JakeFriesen/6502_computer/keyboard_lib.asm

;-----------------------------------------------;
;              Keyboard Library                 ;
;-----------------------------------------------;

; Keyboard pointers
kb_wptr = $0000
kb_rptr = $0001
kb_flags = $0002

; 256-byte kb buffer 0200-02ff
kb_buffer = $0200  


key_pressed:
  ldx kb_rptr
  lda kb_buffer, x
  cmp #$0a           ; enter - go to second line
  beq enter_pressed
  cmp #$1b           ; escape - clear display
  beq esc_pressed

  jsr print_char
  
  lda kb_buffer, x    ;load it again for acia
  jsr print_char_acia

  inc kb_rptr
  jmp loop

enter_pressed:
  lda #%10101000 ; put cursor at position 40
  jsr lcd_instruction
  inc kb_rptr
  jmp loop

esc_pressed:
  lda #%00000001 ; Clear display
  jsr lcd_instruction
  inc kb_rptr
  jmp loop

; IRQ vector points here
keyboard_interrupt:
  pha
  txa
  pha
  lda kb_flags
  and #RELEASE   ; check if we're releasing a key
  beq read_key   ; otherwise, read the key

  lda kb_flags
  eor #RELEASE   ; flip the releasing bit
  sta kb_flags
  lda PORTA      ; read key value that's being released
  cmp #$12       ; left shift
  beq shift_up
  cmp #$59       ; right shift
  beq shift_up
  jmp exit

shift_up:
  lda kb_flags
  eor #SHIFT  ; flip the shift bit
  sta kb_flags
  jmp exit

read_key:
  lda PORTA
  cmp #$f0        ; if releasing a key
  beq key_release ; set the releasing bit
  cmp #$12        ; left shift
  beq shift_down
  cmp #$59        ; right shift
  beq shift_down

  tax
  lda kb_flags
  and #SHIFT
  bne shifted_key

  lda keymap, x   ; map to character code
  jmp push_key

shifted_key:
  lda keymap_shifted, x   ; map to character code

push_key:
  ldx kb_wptr
  sta kb_buffer, x
  inc kb_wptr
  jmp exit

shift_down:
  lda kb_flags
  ora #SHIFT
  sta kb_flags
  jmp exit

key_release:
  lda kb_flags
  ora #RELEASE
  sta kb_flags

exit:
  pla
  tax
  pla
  rti



  .RODATA
keymap:
  .byte "????????????? `?" ; 00-0F
  .byte "?????q1???zsaw2?" ; 10-1F
  .byte "?cxde43?? vftr5?" ; 20-2F
  .byte "?nbhgy6???mju78?" ; 30-3F
  .byte "?,kio09??./l;p-?" ; 40-4F
  .byte "??'?[=????",$0a,"]?\??" ; 50-5F
  .byte "?????????1?47???" ; 60-6F
  .byte "0.2568",$1b,"??+3-*9??" ; 70-7F
  .byte "????????????????" ; 80-8F
  .byte "????????????????" ; 90-9F
  .byte "????????????????" ; A0-AF
  .byte "????????????????" ; B0-BF
  .byte "????????????????" ; C0-CF
  .byte "????????????????" ; D0-DF
  .byte "????????????????" ; E0-EF
  .byte "????????????????" ; F0-FF
keymap_shifted:
  .byte "????????????? ~?" ; 00-0F
  .byte "?????Q!???ZSAW@?" ; 10-1F
  .byte "?CXDE#$?? VFTR%?" ; 20-2F
  .byte "?NBHGY^???MJU&*?" ; 30-3F
  .byte "?<KIO)(??>?L:P_?" ; 40-4F
  .byte "????{+?????}?|??" ; 50-5F
  .byte "?????????1?47???" ; 60-6F
  .byte "0.2568???+3-*9??" ; 70-7F
  .byte "????????????????" ; 80-8F
  .byte "????????????????" ; 90-9F
  .byte "????????????????" ; A0-AF
  .byte "????????????????" ; B0-BF
  .byte "????????????????" ; C0-CF
  .byte "????????????????" ; D0-DF
  .byte "????????????????" ; E0-EF
  .byte "????????????????" ; F0-FF
